Xmen097/Konzole/Konzole - modely/joystick_bottom.stl

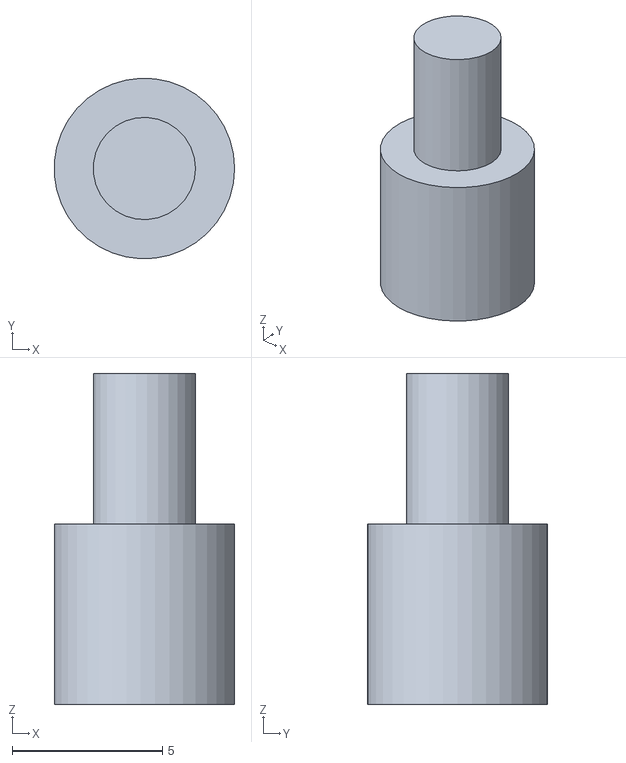
[picture p22: CAD file, 2023-07-13]
Konzole - modely/joystick_bottom.stl
5.99 x 6.00 x 11.0
