Xmen097/Konzole/export/tlacitka_akcni.stl

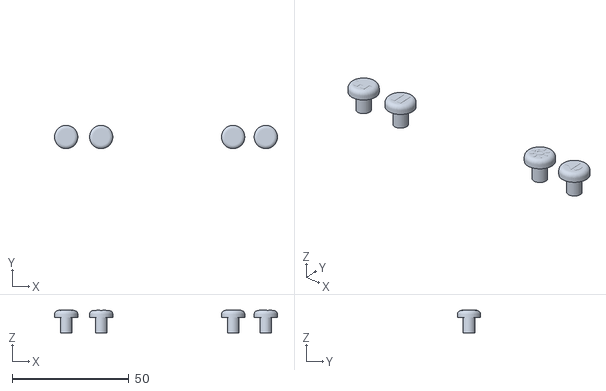
[picture p23: CAD file, 2023-07-13]
export/tlacitka_akcni.stl
95.5 x 9.98 x 9.70
