Xmen097/Konzole/export/joystick_prostredek.stl

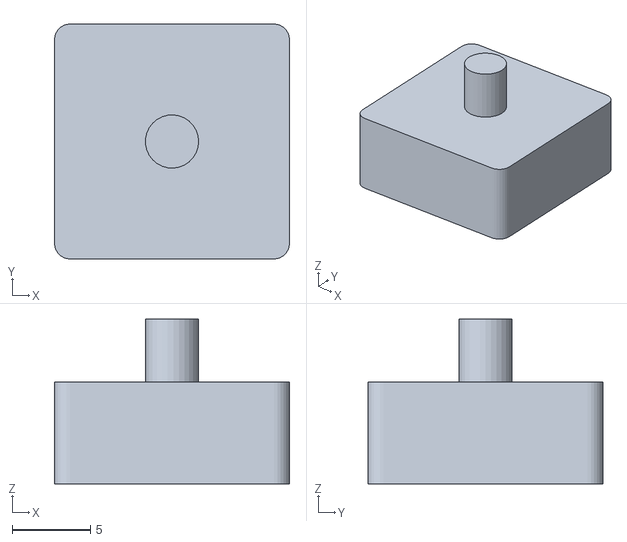
[picture p24: CAD file, 2023-07-13]
export/joystick_prostredek.stl
15.0 x 15.0 x 10.5
