Xmen097/Konzole/Konzole - arduino/Konzole/menu.cpp

#include "define.h"

namespace menu {

  struct Item {
    uint8_t (*data)[5]; 
    byte length;
    color_t *colors;
    color_t background;
  };

  const PROGMEM uint8_t pacman_data[][5] = {{10,0,12,0,255},{6,2,4,0,255},{22,2,4,0,255},{4,4,2,0,255},{18,4,4,255,0},{26,4,2,0,255},{2,6,2,0,255},{28,6,2,0,255},{2,8,2,255,0},{18,8,4,0,255},{4,10,4,255,0},{30,10,2,0,255},{8,12,4,255,0},{12,14,4,255,0},{12,18,4,0,255},{8,20,4,0,255},{4,22,4,0,255},{30,22,2,255,0},{2,24,2,0,255},{2,26,2,255,0},{28,26,2,255,0},{4,28,2,255,0},{26,28,2,255,0},{6,30,4,255,0},{22,30,4,255,0},{10,32,12,255,0}};
  const PROGMEM color_t pacman_colors[] = {65285};   
  Item pacman {pacman_data, 26, pacman_colors, color_dark_purple};

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
  const PROGMEM color_t mario_colors[] = {55616,29249,60867,8452,475,64711};
  Item mario {mario_data, 63, mario_colors, color_blue};

  const PROGMEM uint8_t pong_data[][5] = {{2,6,4,0,255},{26,6,4,0,255},{21,17,2,0,255},{21,19,2,255,0},{2,26,4,255,0},{26,26,4,255,0}};
  const PROGMEM color_t pong_colors[] = {61309};
  Item pong {pong_data, 6, pong_colors, color_blue};

  const byte icon_count = 6;
  const Item icons[] = {pacman, pong , snake, shooter, tetris, settings};

  uint8_t menu_position;
  uint8_t scroll_position;

  void drawScroll() {
    if(scroll_position != 0) {
      tft.fillTriangle(120, 55, 200, 55, 160, 35, color_gray);
      tft.fillTriangle(140, 50, 180, 50, 160, 40, color_white);
    } else {
      int i=35;
      uint8_t colBlue = 31 - i/8;
      uint8_t colGreen = 0 + i/4;
      uint8_t colRed = 0 + i/16;
      for (; i<=55; i++) {
        colBlue -= ((i % 8) == 0);
        colGreen += ((i % 4) == 0);
        colRed += ((i % 16) == 0);
        uint16_t color = ((uint16_t) (colRed & 0b00011111) << 11) + ((uint16_t)(colGreen & 0b00111111) << 5) + (colBlue & 0b00011111);
        tft.drawHLine(120, i, 81, color);
      }
    }
    if (scroll_position != icon_count-6) {
      tft.fillTriangle(120, 220, 200, 220, 160, 240, color_gray);
      tft.fillTriangle(140, 225, 180, 225, 160, 235, color_white);
    } else {
      int i=220;
      uint8_t colBlue = 31 - i/8;
      uint8_t colGreen = 0 + i/4;
      uint8_t colRed = 0 + i/16;
      for (; i<=240; i++) {
        colBlue -= ((i % 8) == 0);
        colGreen += ((i % 4) == 0);
        colRed += ((i % 16) == 0);
        uint16_t color = ((uint16_t) (colRed & 0b00011111) << 11) + ((uint16_t)(colGreen & 0b00111111) << 5) + (colBlue & 0b00011111);
        tft.drawHLine(120, i, 81, color);
      }
    }
  }
  
  void drawBatteryIcon() {
    const static PROGMEM byte row1[14] = {0b00000000, 0b00000000, 0b00000000, 0b00000000, 0b00000000, 0b11000000, 0b11000000, 0b11000000, 0b11000000, 0b00000000, 0b00000000, 0b00000000, 0b00000000, 0b00000000};
    const static PROGMEM byte row2[14] = {0b11111111, 0b11111111, 0b00000011, 0b00000011, 0b00000011, 0b00000011, 0b00000011, 0b10000011, 0b11000011, 0b01100011, 0b00000011, 0b00000011, 0b11111111, 0b11111111};
    const static PROGMEM byte row3[14] = {0b11111111, 0b11111111, 0b00000000, 0b00000000, 0b10001100, 0b11001110, 0b01101111, 0b00111101, 0b00011100, 0b00001100, 0b00000000, 0b00000000, 0b11111111, 0b11111111};
    const static PROGMEM byte row4[14] = {0b00111111, 0b00111111, 0b00110000, 0b00110000, 0b00110001, 0b00110000, 0b00110000, 0b00110000, 0b00110000, 0b00110000, 0b00110000, 0b00110000, 0b00111111, 0b00111111};
    byte *rows[] = {row1, row2, row3, row4};
    for (byte r=0; r<4; r++) {
      for (byte i=0; i<14; i++) {
        byte data = pgm_read_byte_near(rows[r]+i);
        for (byte x=0; x<8; x++) {
          if (data&1<<x)
            tft.drawPixel(i+240,8*r+x-4, color_black);
        }
      }
    }
}

  void drawBackground() {
    uint8_t colBlue = 31;
    uint8_t colGreen = 0;
    uint8_t colRed = 0;
    for (int i = 0; i < 240; i++) {
      colBlue -= ((i % 8) == 0);
      colGreen += ((i % 4) == 0);
      colRed += ((i % 16) == 0);

      uint16_t color = ((uint16_t) (colRed & 0b00011111) << 11) + ((uint16_t)(colGreen & 0b00111111) << 5) + (colBlue & 0b00011111);
      tft.drawHLine(0, i, 320, color);
    }

    tft.fillRoundRect(0, -30, 320, 60, 30, color_white);
    tft.setCursor(96, 10);
    tft.setTextColor(color_black);
    tft.setTextSize(2);
    tft.print(F("Hlavni menu"));
    drawBatteryIcon();
  }

  void drawItem(int position) {
    int y = position/3;
    int x = position - y*3;
    if (position+scroll_position == menu_position) {
      tft.fillRoundRect(40+90*x, 65+85*y, 60, 60, 7, color_yellow);
    } else {
      tft.fillRoundRect(40+90*x, 65+85*y, 60, 60, 7, color_black);
    }
    tft.fillRoundRect(45+90*x, 70+85*y, 50, 50, 7, icons[position+scroll_position].background);
    draw_image(54+90*x, 79+85*y, icons[position+scroll_position].data, icons[position+scroll_position].length, icons[position+scroll_position].colors, 32, icons[position+scroll_position].background);
  }

  void drawItems() {
    for (int i=0; i<6; i++) {
      drawItem(i);
    }
  }

  void selectMenuItem() {
    current_game = menu_position+1;  
    game_setups[current_game]();
  }
  
  void setup() {
    menu_position = 0;
    scroll_position = 0;
    drawBackground();
    drawItems();
    drawScroll();
  }

  void destruct() {
    
  }

  void loop() {
    static byte last_battery = -2;
    byte new_battery = get_battery();
    if (last_battery != new_battery) {
      last_battery = new_battery;
      tft.fillRect(260, 0, 45, 24, color_white);
      tft.setCursor(260, 10);
      tft.setTextColor(color_black);
      tft.setTextSize(2);
      if (last_battery != 255) {
        char reading_text[3];
        itoa(last_battery,reading_text,10);
        tft.print(reading_text);
        tft.print("%");
      } else {
        tft.print("USB");
      }
    }
    if (Input::is_just_pressed(button_down)) {
      selectMenuItem();
    }
    if (Input::is_just_pressed(dpad_down) && menu_position+3 < icon_count) {
      menu_position += 3;
      if (menu_position >= scroll_position+6) {
        scroll_position+=3;
        drawScroll();
        drawItems();
      }
      drawItem(menu_position-3-scroll_position);
      drawItem(menu_position-scroll_position);
    }
    if (Input::is_just_pressed(dpad_up) && menu_position-3 >= 0) {
      menu_position -= 3;
      if (menu_position < scroll_position) {
        scroll_position-=3;
        drawScroll();
        drawItems();
      }
      drawItem(menu_position+3-scroll_position);
      drawItem(menu_position-scroll_position);
    }
    if (Input::is_just_pressed(dpad_left) && menu_position-1 >= 0) {
      menu_position -= 1;
      if (menu_position < scroll_position) {
        scroll_position-=3;
        drawScroll();
        drawItems();
      }
      drawItem(menu_position+1-scroll_position);
      drawItem(menu_position-scroll_position);
    }
    if (Input::is_just_pressed(dpad_right) && menu_position+1 < icon_count) {
      menu_position += 1;
      if (menu_position >= scroll_position+6) {
        scroll_position+=3;
        drawScroll();
        drawItems();
      }
      drawItem(menu_position-1-scroll_position);
      drawItem(menu_position-scroll_position);
    }
  }
}
